YSantoni/Switchophorese/Code/SwitchophoreseHB2/bitmaps.h

#ifndef BITMAPS_H
#define BITMAPS_H

const uint16_t vulcain[] PROGMEM = {
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
};
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
